Method-Inc-OLD/method-pfc_physical-build/Documentation/Photos/side-module.jpg

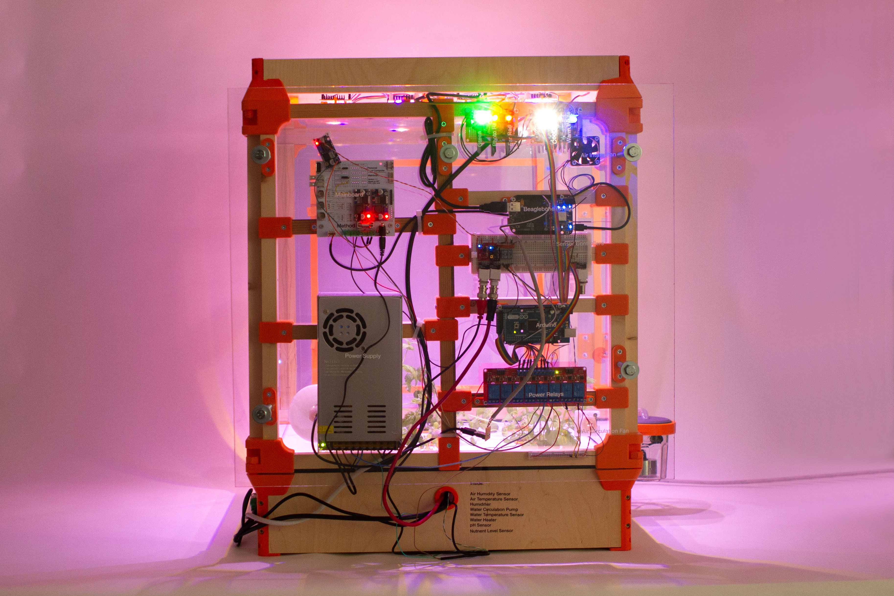
Documentation/Photos/side-module.jpg
