Method-Inc-OLD/method-pfc_physical-build/Documentation/~Working Files/pfc-back-view.jpg

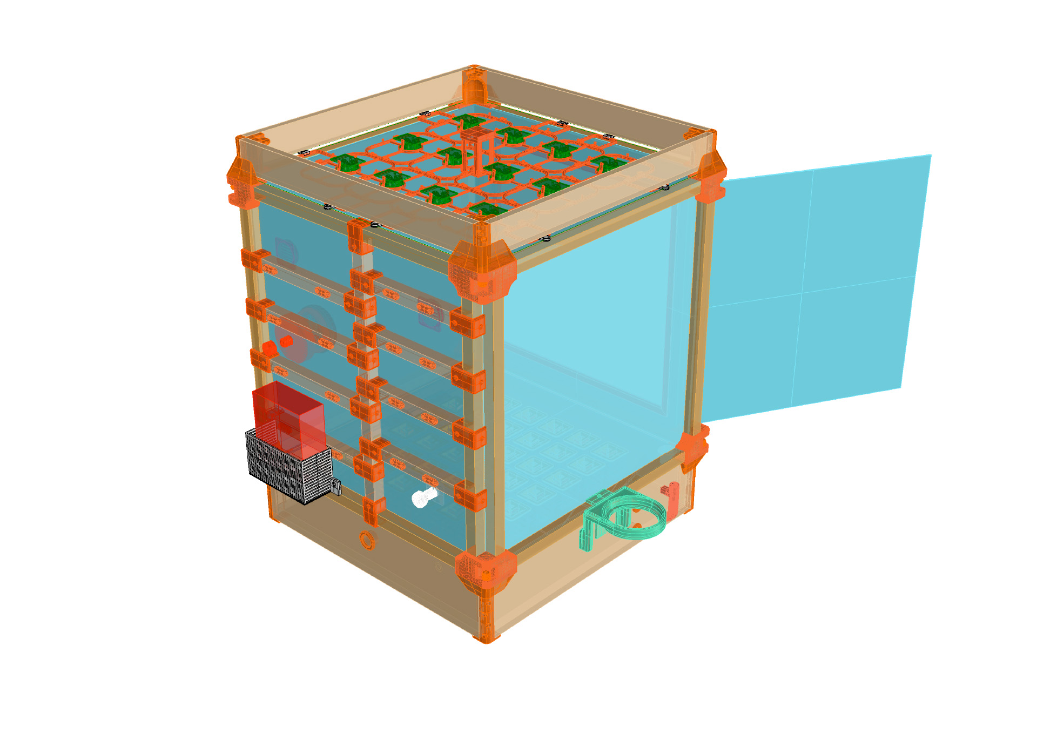
Documentation/~Working Files/pfc-back-view.jpg
