Method-Inc-OLD/method-pfc_physical-build/Documentation/~Working Files/pfc-front-view.jpg

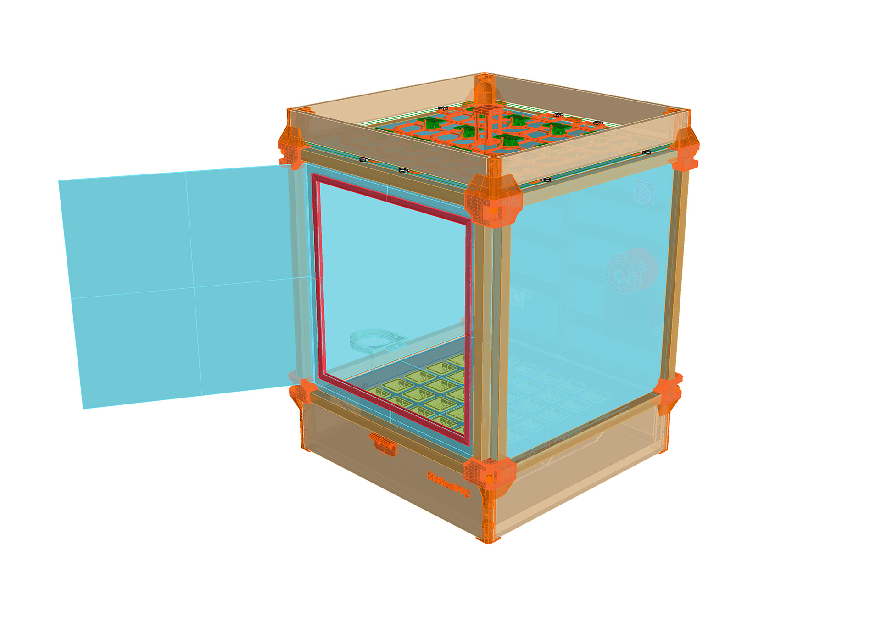
Documentation/~Working Files/pfc-front-view.jpg
