Method-Inc-OLD/method-pfc_physical-build/Electrical/Air Sensor/Air Sensor Schematic.png

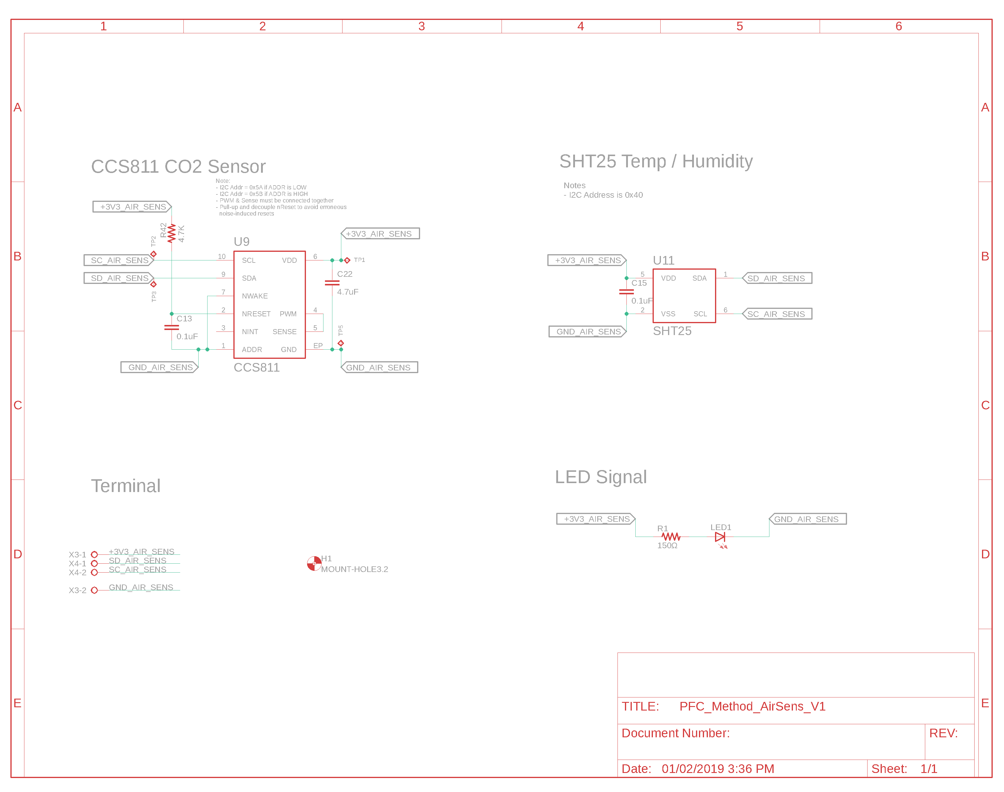
Electrical/Air Sensor/Air Sensor Schematic.png
