Method-Inc-OLD/method-pfc_physical-build/Electrical/Lighting Node + Driver/Lighting Node + Driver Schematic.png

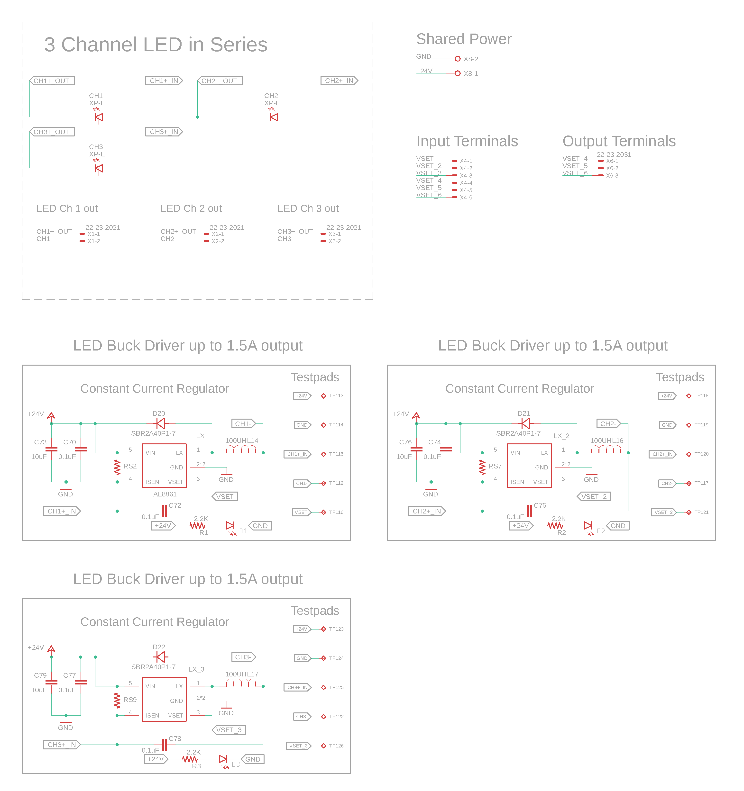
Electrical/Lighting Node + Driver/Lighting Node + Driver Schematic.png
