Method-Inc-OLD/method-pfc_physical-build/Electrical/Lighting Node/Lighting Node Schematic.png

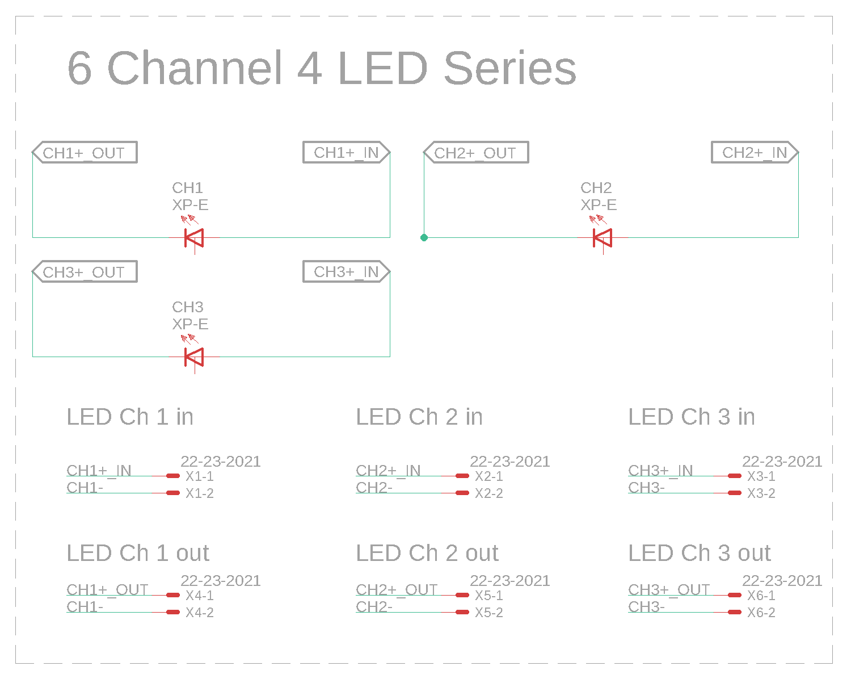
Electrical/Lighting Node/Lighting Node Schematic.png
