Method-Inc-OLD/method-pfc_physical-build/Electrical/Mainboard/Mainboard Schematic.png

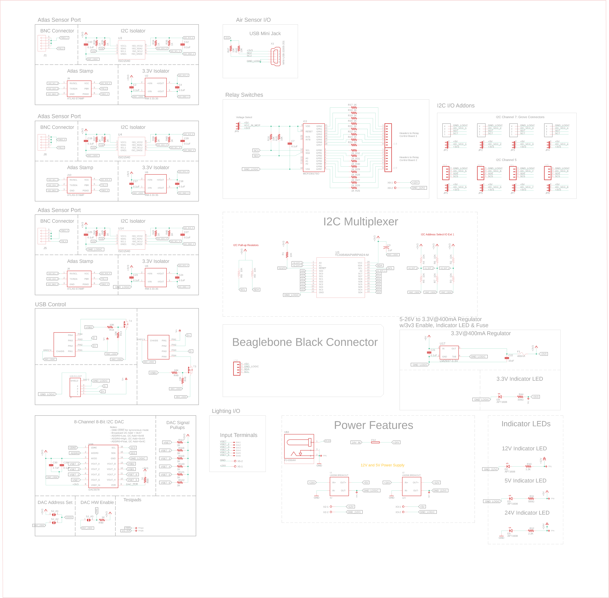
Electrical/Mainboard/Mainboard Schematic.png
