Method-Inc-OLD/method-pfc_physical-build/Mechanical/Middle Module/STL for 3D printing/M.05 - Circulation Fan Mount (2 of 2).stl

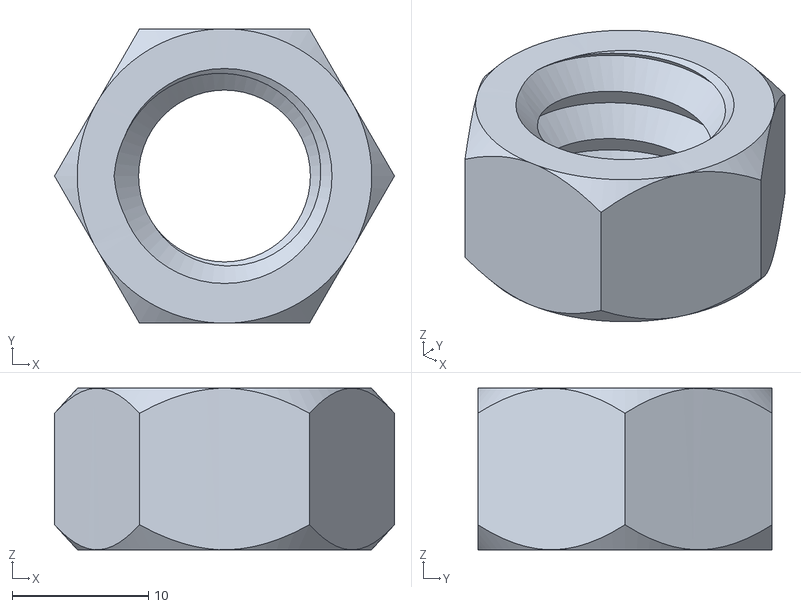
[picture p29: CAD file, 2019-05-31]
Mechanical/Middle Module/STL for 3D printing/M.05 - Circulation Fan Mount (2 of 2).stl
24.9 x 21.6 x 11.8
