Method-Inc-OLD/method-pfc_physical-build/Mechanical/Middle Module/STL for 3D printing/M.07 - Door Lock /files/Fecho_001-16.stl

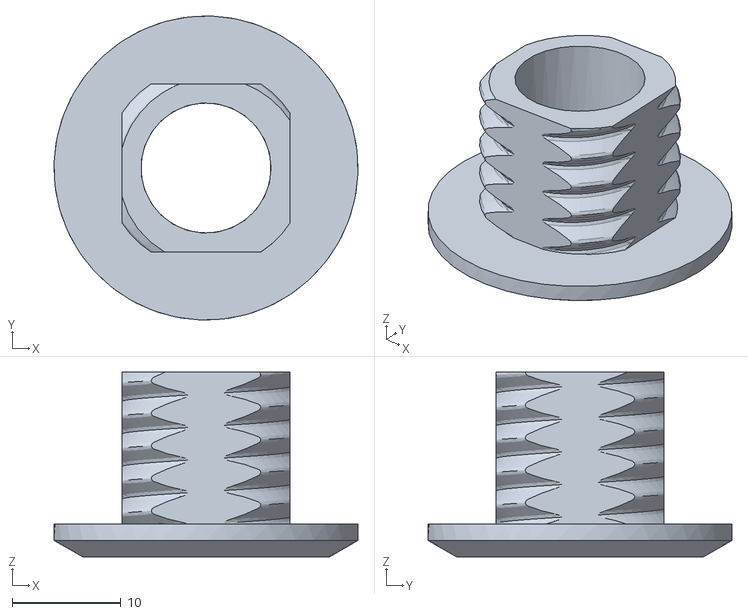
[picture p30: CAD file, 2019-05-31]
Mechanical/Middle Module/STL for 3D printing/M.07 - Door Lock /files/Fecho_001-16.stl
28.0 x 28.0 x 17.0
