Method-Inc-OLD/method-pfc_physical-build/Mechanical/Top Module/STL for 3D Printing/T.01 - Top Corner Connector.stl

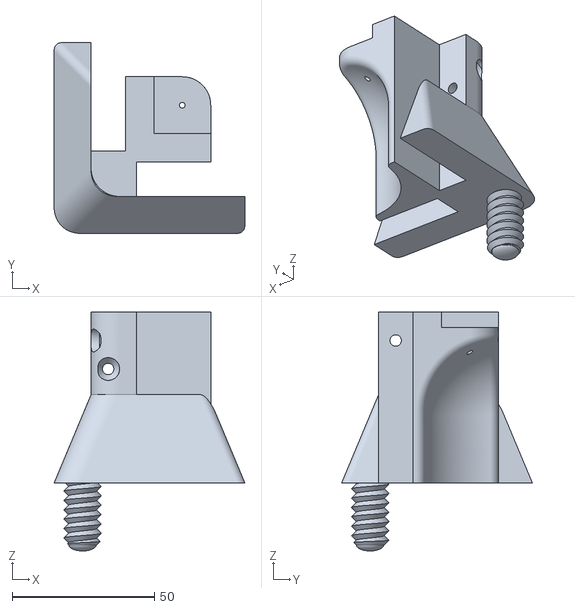
[picture p31: CAD file, 2019-05-31]
Mechanical/Top Module/STL for 3D Printing/T.01 - Top Corner Connector.stl
67.0 x 67.0 x 83.9
