Method-Inc-OLD/method-pfc_physical-build/Mechanical/Bottom Module/STL for 3D Printing/B.02.B - Bottom Corner Connector, Door, Right (1 of 2).stl

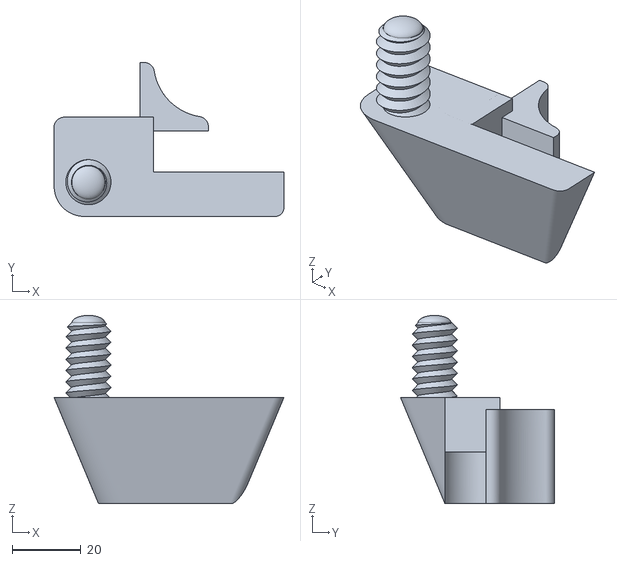
[picture p32: CAD file, 2019-05-31]
Mechanical/Bottom Module/STL for 3D Printing/B.02.B - Bottom Corner Connector, Door, Right (1 of 2).stl
67.1 x 45.0 x 54.9
