Method-Inc-OLD/method-pfc_physical-build/Mechanical/Middle Module/STL for 3D printing/M.01 - Middle Corner Connector.stl

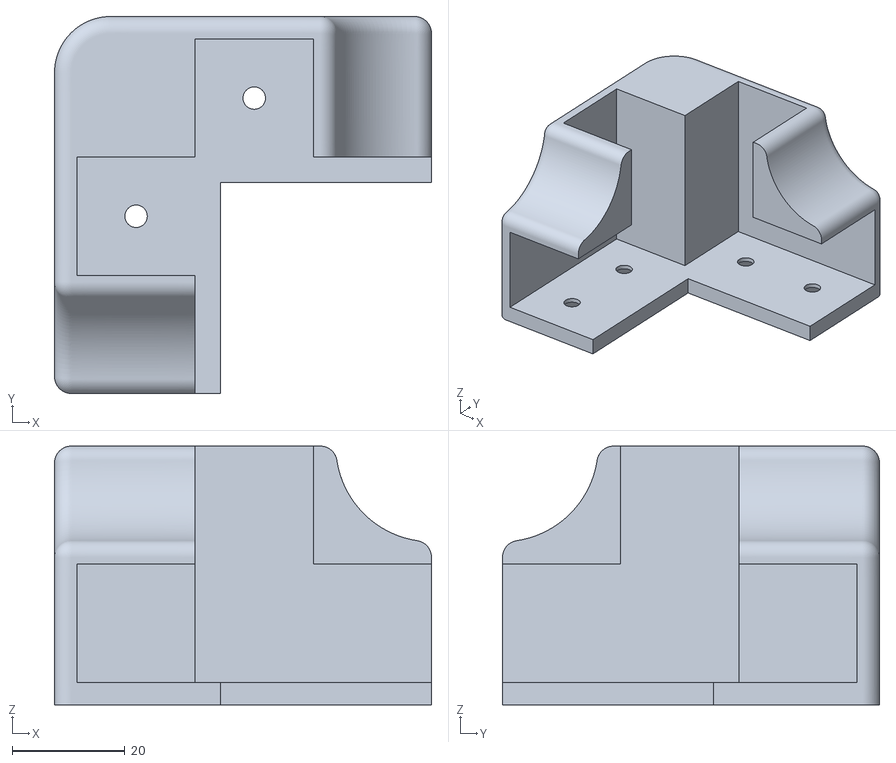
[picture p33: CAD file, 2019-05-31]
Mechanical/Middle Module/STL for 3D printing/M.01 - Middle Corner Connector.stl
67.0 x 67.0 x 46.0
