Method-Inc-OLD/method-pfc_physical-build/Mechanical/Middle Module/STL for 3D printing/M.07 - Door Lock /files/Fecho_002-16.stl

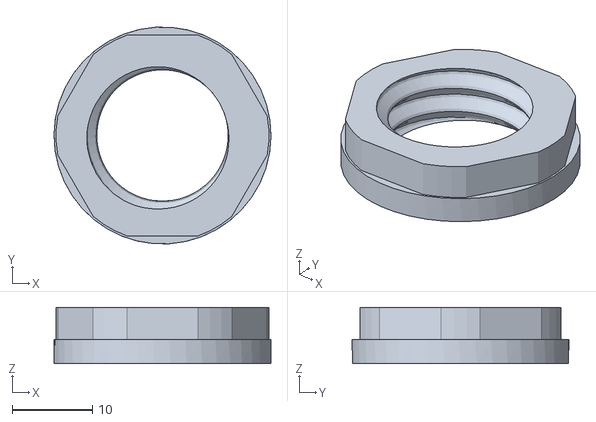
[picture p34: CAD file, 2019-05-31]
Mechanical/Middle Module/STL for 3D printing/M.07 - Door Lock /files/Fecho_002-16.stl
27.0 x 26.9 x 7.00
