Method-Inc-OLD/method-pfc_physical-build/Mechanical/Top Module/STL for 3D Printing/T.02.B - Lighting Board Mount, Camera Holder.stl

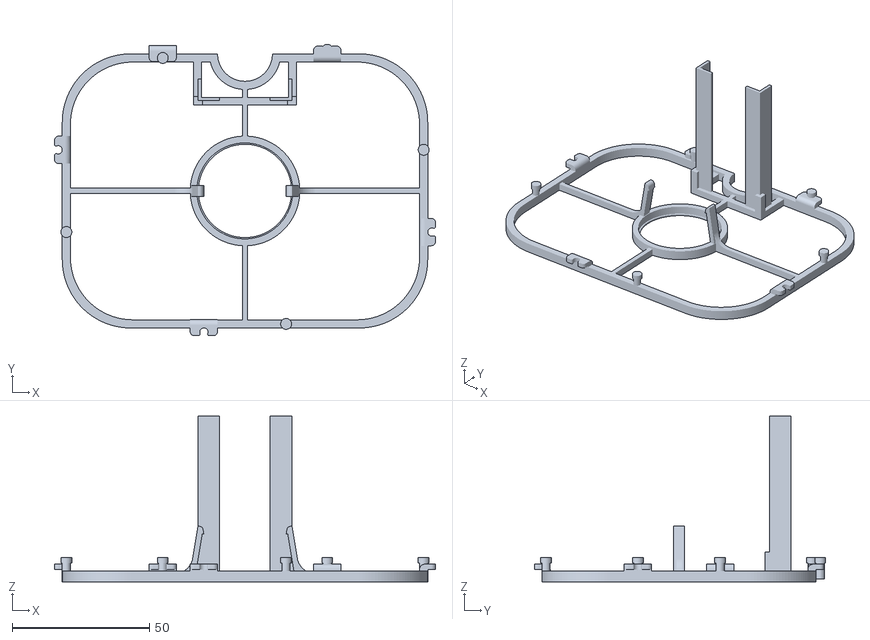
[picture p35: CAD file, 2019-05-31]
Mechanical/Top Module/STL for 3D Printing/T.02.B - Lighting Board Mount, Camera Holder.stl
139.0 x 106.3 x 60.5
