Method-Inc-OLD/method-pfc_physical-build/Mechanical/Bottom Module/STL for 3D Printing/B.07 - Atlas Sensor Holder.stl

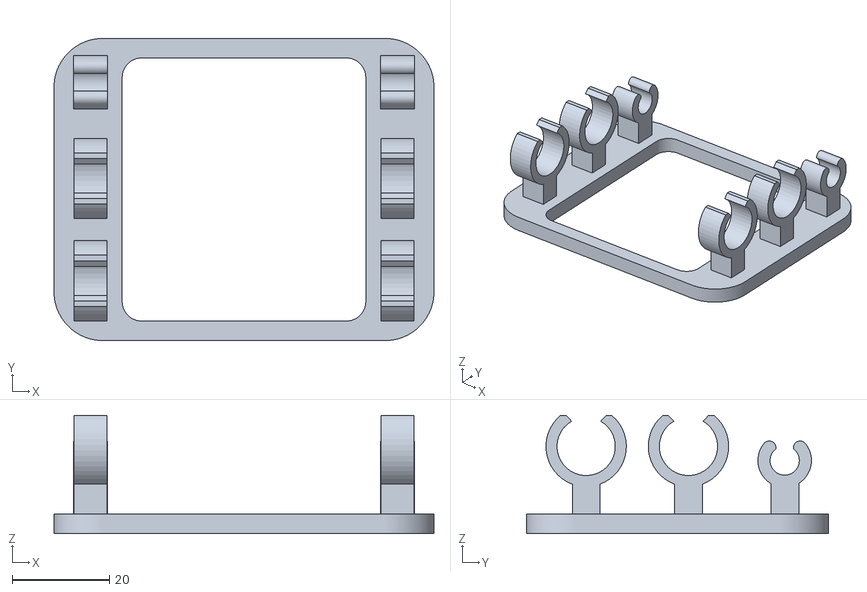
[picture p36: CAD file, 2019-05-31]
Mechanical/Bottom Module/STL for 3D Printing/B.07 - Atlas Sensor Holder.stl
78.0 x 62.0 x 24.3
