Method-Inc-OLD/method-pfc_physical-build/Mechanical/Middle Module/STL for 3D printing/M.03.C - Frame Edge, Bottom Right.stl

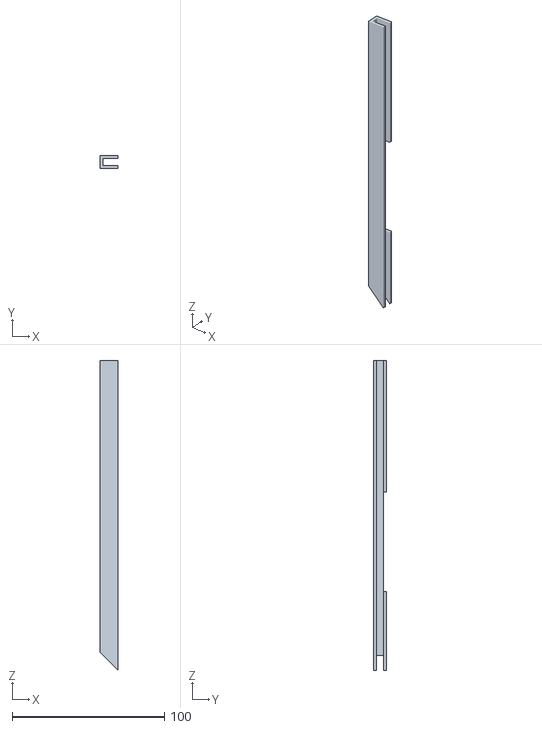
[picture p37: CAD file, 2019-05-31]
Mechanical/Middle Module/STL for 3D printing/M.03.C - Frame Edge, Bottom Right.stl
12.0 x 8.60 x 203.5
