Method-Inc-OLD/method-pfc_physical-build/Mechanical/Middle Module/STL for 3D printing/M.07 - Door Lock /files/Fecho_003.stl

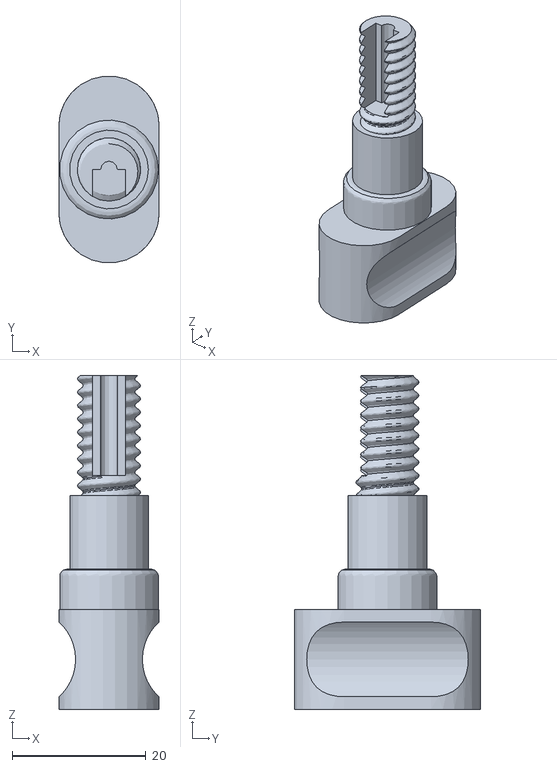
[picture p38: CAD file, 2019-05-31]
Mechanical/Middle Module/STL for 3D printing/M.07 - Door Lock /files/Fecho_003.stl
15.0 x 27.9 x 50.0
