Method-Inc-OLD/method-pfc_physical-build/Mechanical/Top Module/STL for 3D Printing/T.02.A - Lighting Board Mount.stl

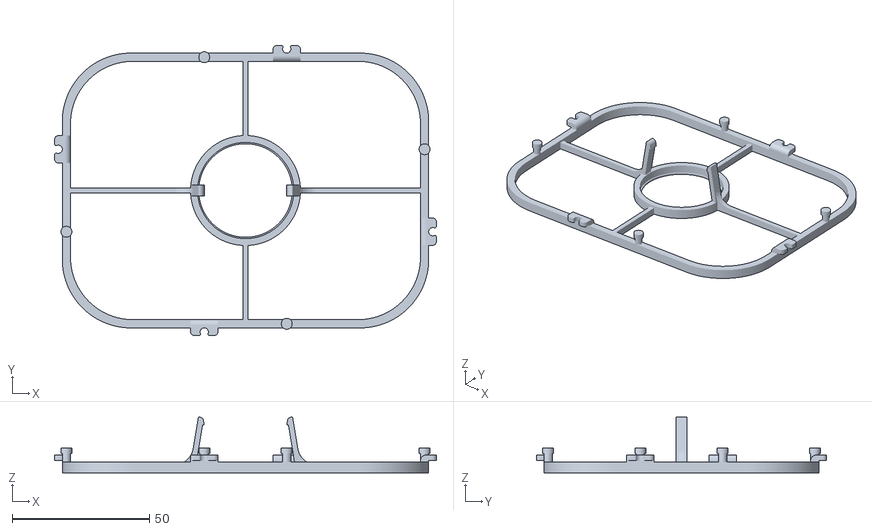
[picture p39: CAD file, 2019-05-31]
Mechanical/Top Module/STL for 3D Printing/T.02.A - Lighting Board Mount.stl
139.0 x 105.6 x 20.3
