Method-Inc-OLD/method-pfc_physical-build/Mechanical/Bottom Module/STL for 3D Printing/B.01.A - Bottom Corner Connector, Left (1 of 2).stl

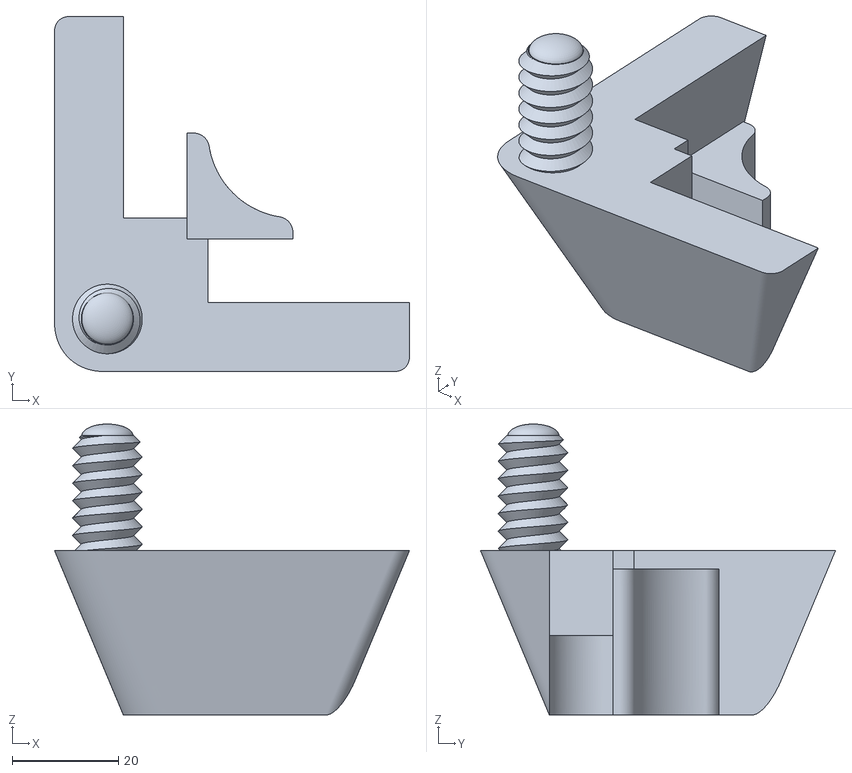
[picture p40: CAD file, 2019-05-31]
Mechanical/Bottom Module/STL for 3D Printing/B.01.A - Bottom Corner Connector, Left (1 of 2).stl
67.0 x 67.0 x 54.9
