Method-Inc-OLD/method-pfc_physical-build/Mechanical/Middle Module/STL for 3D printing/M.07 - Door Lock /files/Fecho_001-18.stl

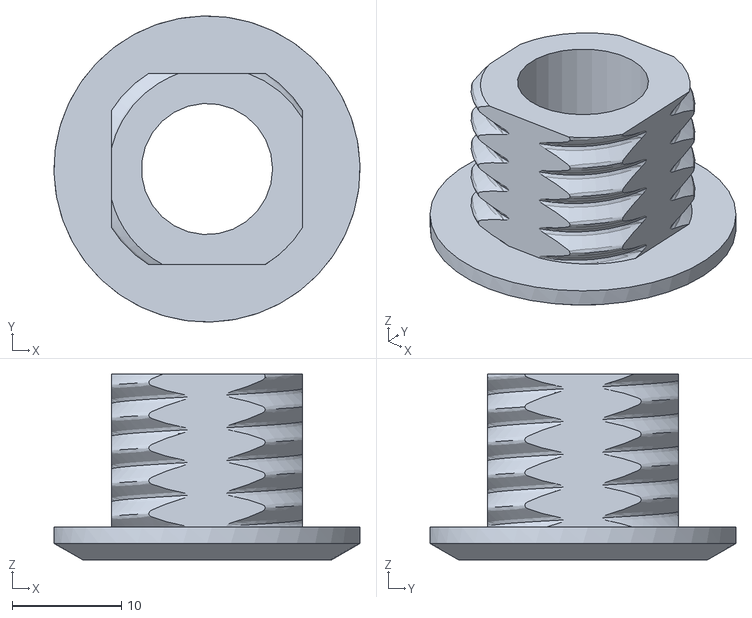
[picture p41: CAD file, 2019-05-31]
Mechanical/Middle Module/STL for 3D printing/M.07 - Door Lock /files/Fecho_001-18.stl
28.0 x 28.0 x 17.0
