Method-Inc-OLD/method-pfc_physical-build/Mechanical/Bottom Module/STL for 3D Printing/B.05v2 - Humidifier Mount (2 of 2).stl

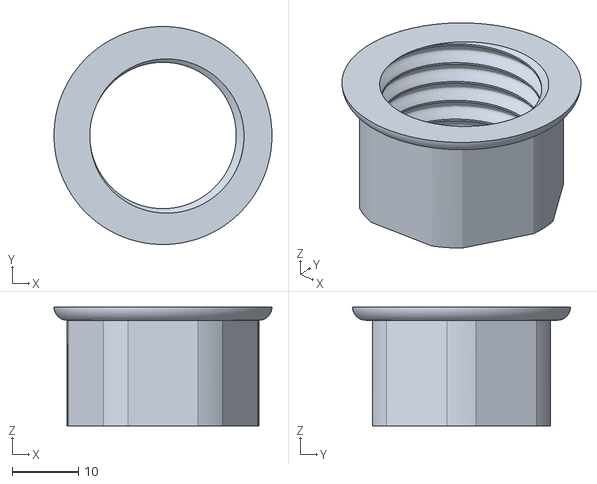
[picture p42: CAD file, 2019-05-31]
Mechanical/Bottom Module/STL for 3D Printing/B.05v2 - Humidifier Mount (2 of 2).stl
33.0 x 33.0 x 18.0
