Method-Inc-OLD/method-pfc_physical-build/Mechanical/Bottom Module/STL for 3D Printing/B.04 - Humidifier Tank Mount.stl

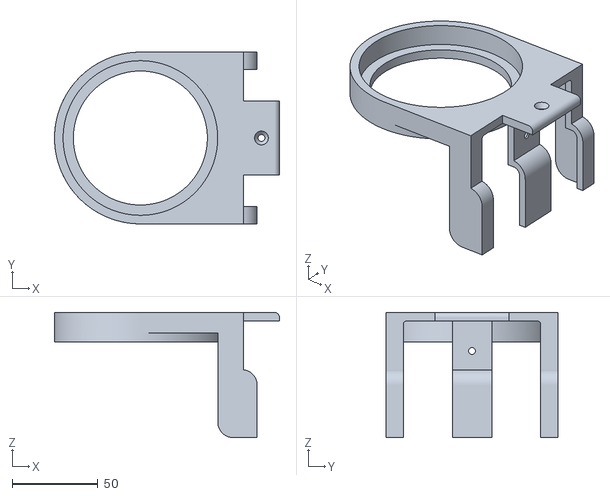
[picture p43: CAD file, 2019-05-31]
Mechanical/Bottom Module/STL for 3D Printing/B.04 - Humidifier Tank Mount.stl
131.0 x 100.0 x 73.0
