Method-Inc-OLD/method-pfc_physical-build/Mechanical/Middle Module/STL for 3D printing/M.07 - Door Lock /files/Fecho_006.stl

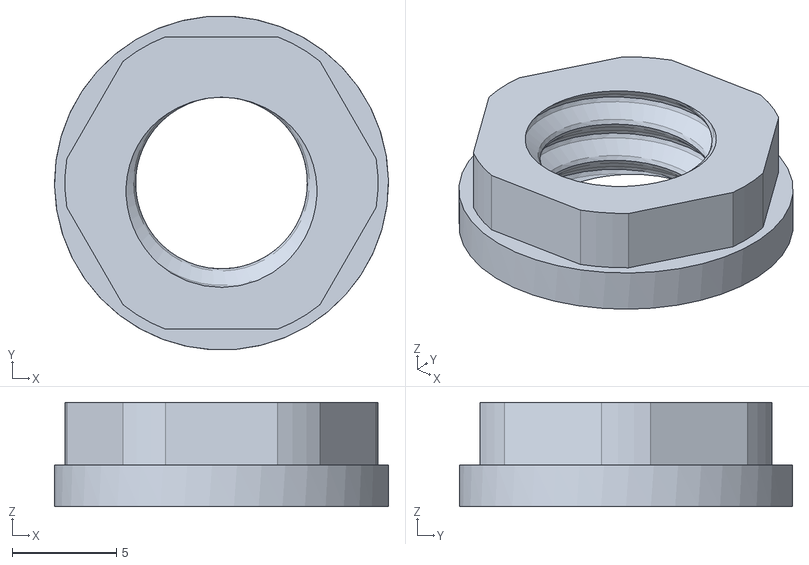
[picture p45: CAD file, 2019-05-31]
Mechanical/Middle Module/STL for 3D printing/M.07 - Door Lock /files/Fecho_006.stl
16.0 x 16.0 x 5.00
