Method-Inc-OLD/method-pfc_physical-build/Mechanical/Bottom Module/STL for 3D Printing/B.11 - Bottom Module – Safety Cover.stl

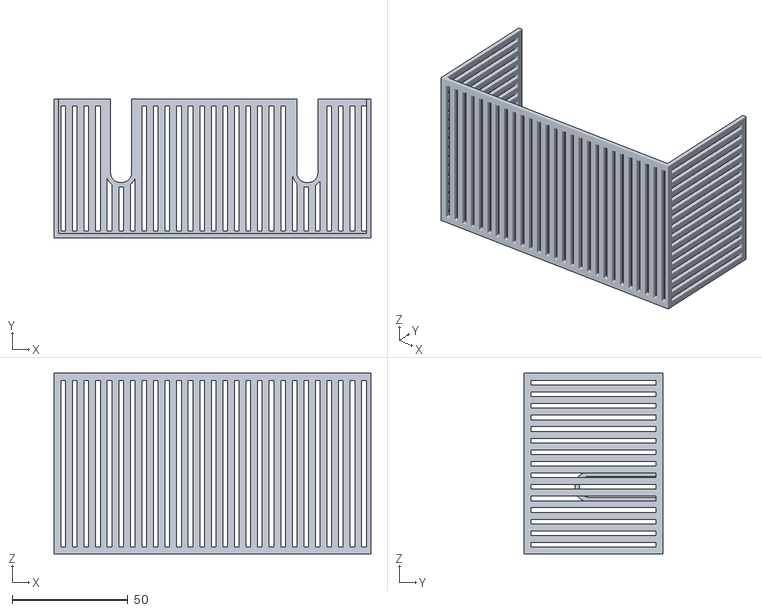
[picture p46: CAD file, 2019-05-31]
Mechanical/Bottom Module/STL for 3D Printing/B.11 - Bottom Module – Safety Cover.stl
137.0 x 60.0 x 78.2
