Method-Inc-OLD/method-pfc_physical-build/Mechanical/Middle Module/STL for 3D printing/M.02 - Air Sensor Bubble (1 of 3).stl

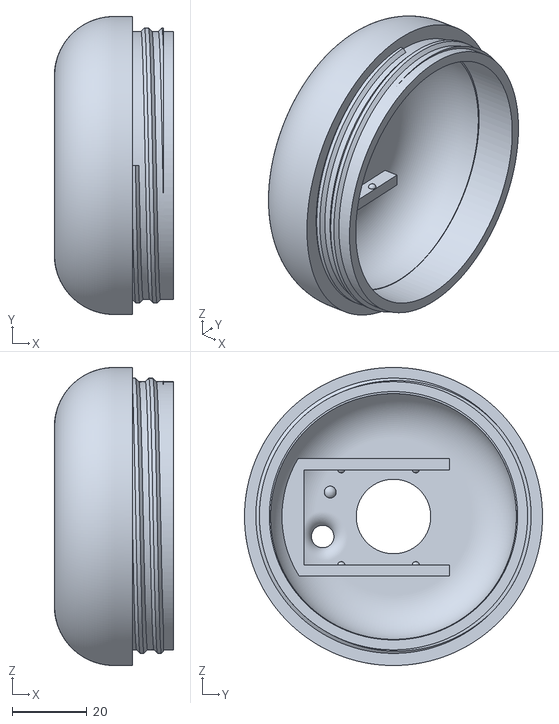
[picture p47: CAD file, 2019-05-31]
Mechanical/Middle Module/STL for 3D printing/M.02 - Air Sensor Bubble (1 of 3).stl
32.0 x 80.0 x 80.0
