Method-Inc-OLD/method-pfc_physical-build/Mechanical/Bottom Module/STL for 3D Printing/B.01.B - Bottom Corner Connector, Right (2 of 2).stl

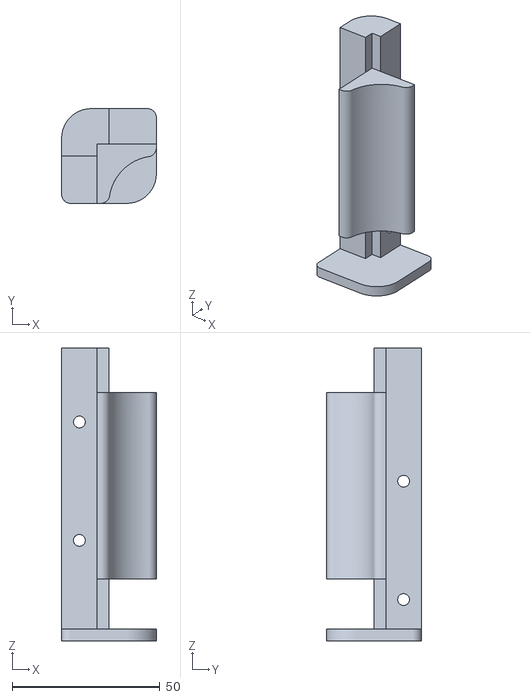
[picture p49: CAD file, 2019-05-31]
Mechanical/Bottom Module/STL for 3D Printing/B.01.B - Bottom Corner Connector, Right (2 of 2).stl
32.0 x 32.0 x 99.0
