Method-Inc-OLD/method-pfc_physical-build/Mechanical/Bottom Module/STL for 3D Printing/B.05v1 - Humidifier Mount (1 of 2).stl

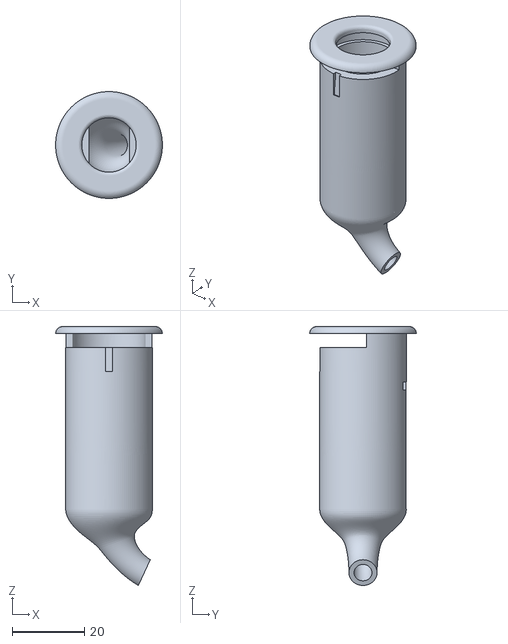
[picture p51: CAD file, 2019-05-31]
Mechanical/Bottom Module/STL for 3D Printing/B.05v1 - Humidifier Mount (1 of 2).stl
29.6 x 29.6 x 71.8
