Method-Inc-OLD/method-pfc_physical-build/Mechanical/Bottom Module/STL for 3D Printing/B.09 - Name plate.stl

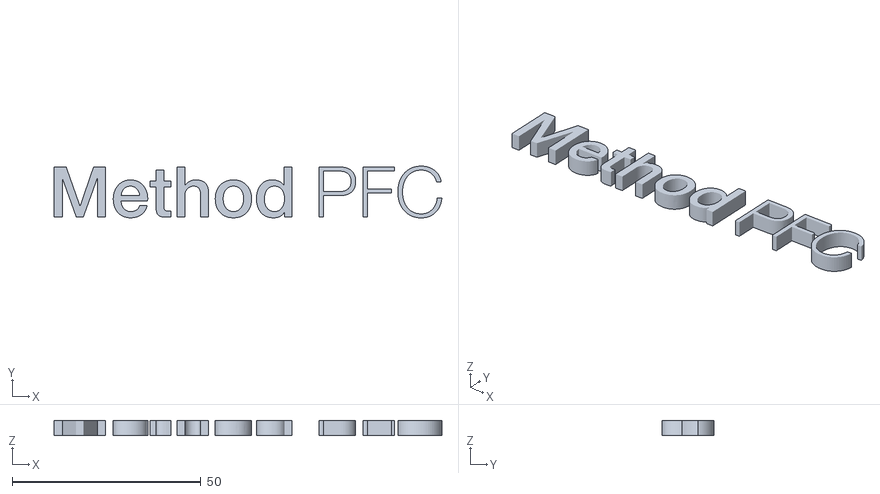
[picture p52: CAD file, 2019-05-31]
Mechanical/Bottom Module/STL for 3D Printing/B.09 - Name plate.stl
102.8 x 13.7 x 4.00
