Method-Inc-OLD/method-pfc_physical-build/Mechanical/Bottom Module/STL for 3D Printing/B.03 - Feeding Tube Holder.stl

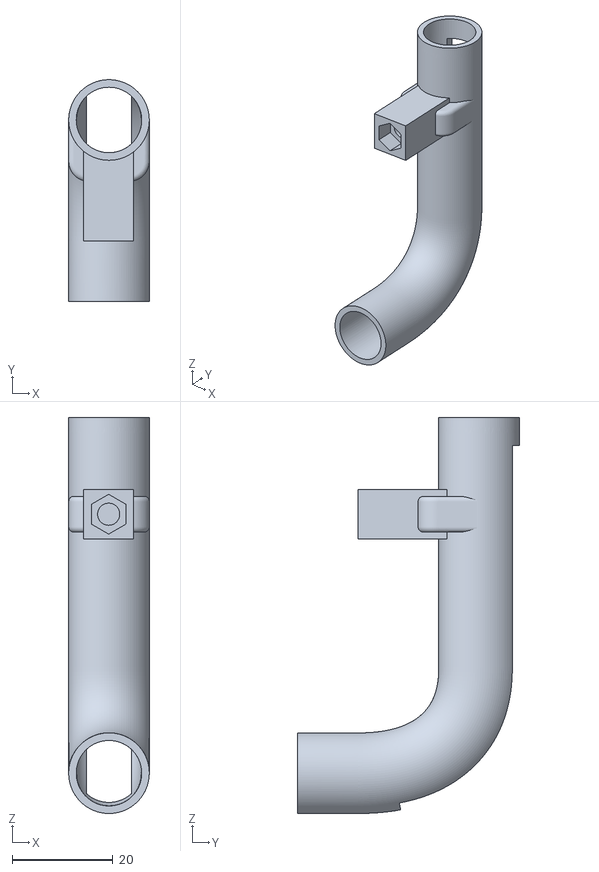
[picture p53: CAD file, 2019-05-31]
Mechanical/Bottom Module/STL for 3D Printing/B.03 - Feeding Tube Holder.stl
16.0 x 44.0 x 78.6
