Method-Inc-OLD/method-pfc_physical-build/Mechanical/Bottom Module/STL for 3D Printing/B.10.B - Rivet, Large, for Wiring.stl

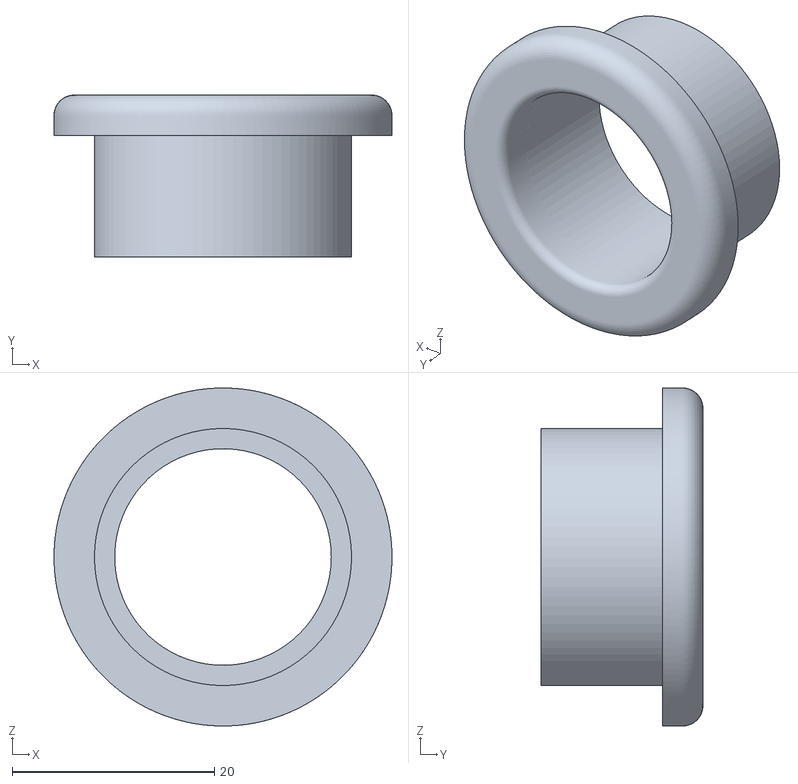
[picture p54: CAD file, 2019-05-31]
Mechanical/Bottom Module/STL for 3D Printing/B.10.B - Rivet, Large, for Wiring.stl
33.4 x 16.0 x 33.4
