Method-Inc-OLD/method-pfc_physical-build/Mechanical/Bottom Module/STL for 3D Printing/B.010.A - Rivet, Small, for Tubing.stl

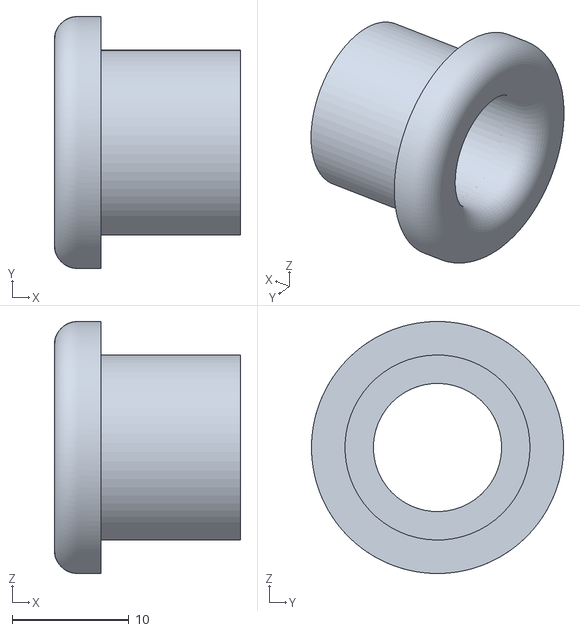
[picture p55: CAD file, 2019-05-31]
Mechanical/Bottom Module/STL for 3D Printing/B.010.A - Rivet, Small, for Tubing.stl
16.0 x 21.6 x 21.6
