Method-Inc-OLD/method-pfc_physical-build/Mechanical/Bottom Module/STL for 3D Printing/B.08 - Door Handle.stl

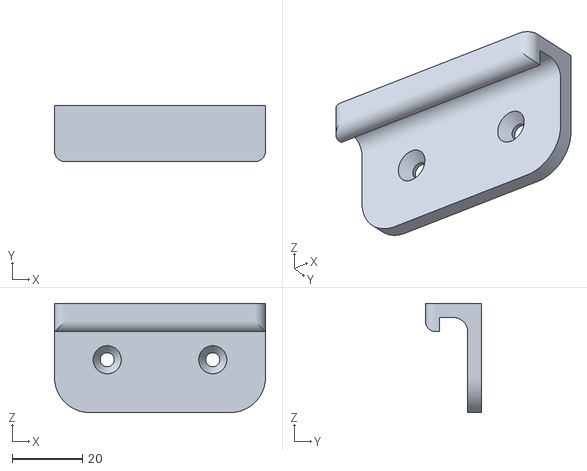
[picture p56: CAD file, 2019-05-31]
Mechanical/Bottom Module/STL for 3D Printing/B.08 - Door Handle.stl
60.0 x 16.0 x 31.0
