Method-Inc-OLD/method-pfc_physical-build/Mechanical/Bottom Module/STL for 3D Printing/B.06 - Rockwool Carriage.stl

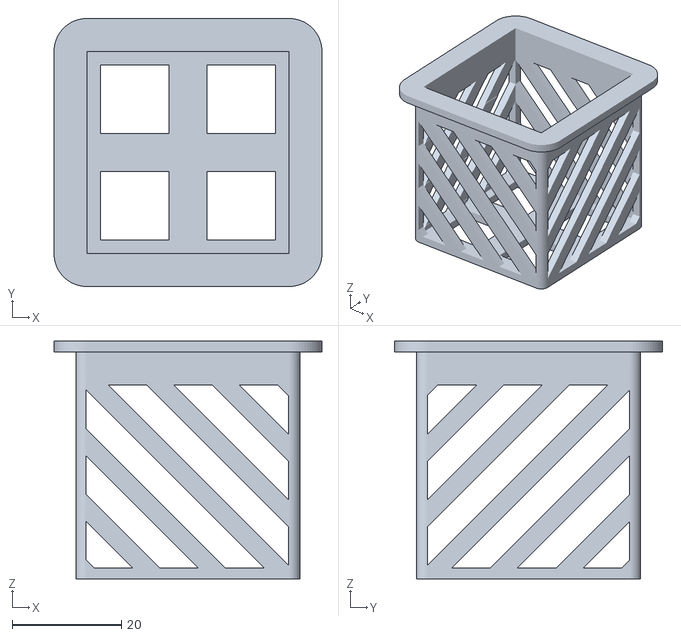
[picture p57: CAD file, 2019-05-31]
Mechanical/Bottom Module/STL for 3D Printing/B.06 - Rockwool Carriage.stl
49.0 x 49.0 x 43.5
