Method-Inc-OLD/method-pfc_physical-build/Mechanical/Bottom Module/STL for 3D Printing/B.05v1 - Humidifier Mount (2 of 2).stl

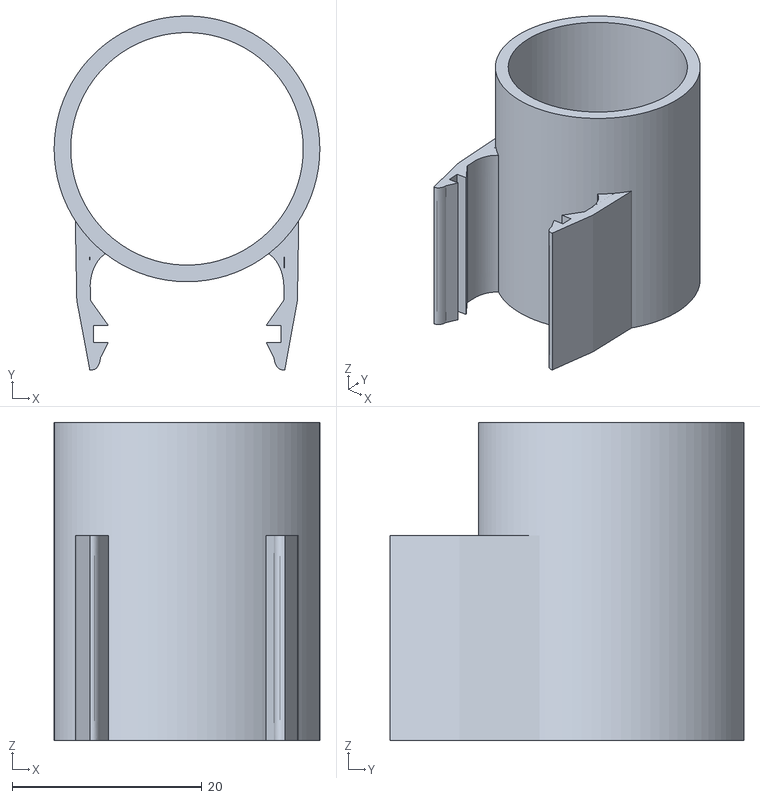
[picture p58: CAD file, 2019-05-31]
Mechanical/Bottom Module/STL for 3D Printing/B.05v1 - Humidifier Mount (2 of 2).stl
28.0 x 37.3 x 33.5
