Method-Inc-OLD/method-pfc_physical-build/Mechanical/Middle Module/STL for 3D printing/M.06 - Door Hinge/images/8f4b54f08936ee00a93d4b04b920801e_preview_featured.jpg

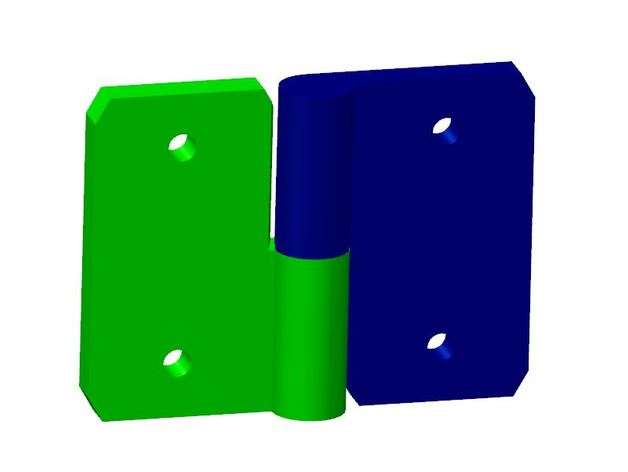
Mechanical/Middle Module/STL for 3D printing/M.06 - Door Hinge/images/8f4b54f08936ee00a93d4b04b920801e_preview_featured.jpg
