Method-Inc-OLD/method-pfc_physical-build/Mechanical/Middle Module/STL for 3D printing/M.06 - Door Hinge/images/fa78f0b6158e9a1c80da4dba1ec0081e_preview_featured.jpg

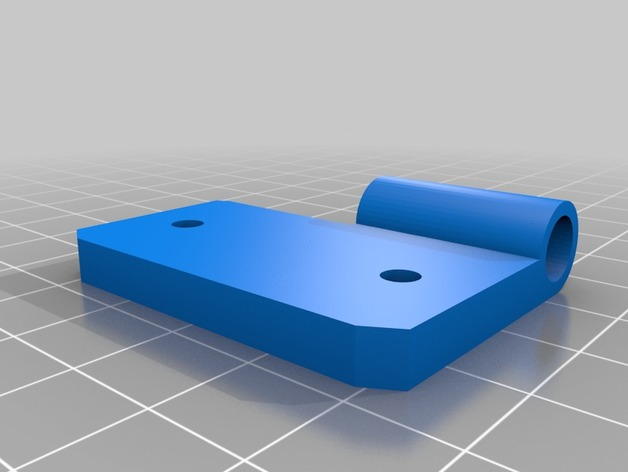
Mechanical/Middle Module/STL for 3D printing/M.06 - Door Hinge/images/fa78f0b6158e9a1c80da4dba1ec0081e_preview_featured.jpg
