Method-Inc-OLD/method-pfc_physical-build/Mechanical/Middle Module/STL for 3D printing/M.07 - Door Lock /images/0bf5f9f50b0dcd644b62373efc88d2cc_preview_featured.jpg

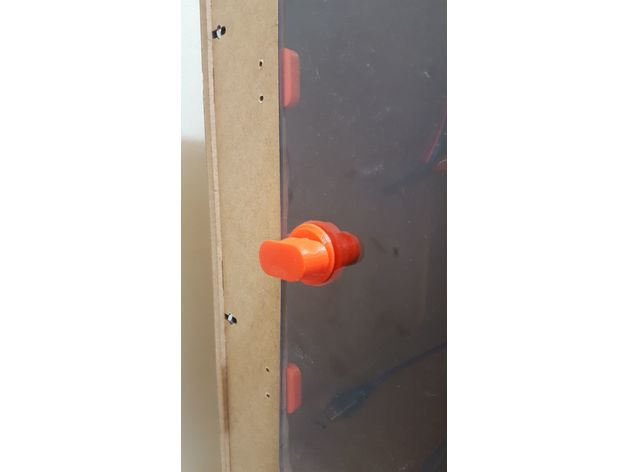
Mechanical/Middle Module/STL for 3D printing/M.07 - Door Lock /images/0bf5f9f50b0dcd644b62373efc88d2cc_preview_featured.jpg
