Method-Inc-OLD/method-pfc_physical-build/Mechanical/Middle Module/STL for 3D printing/M.07 - Door Lock /images/1bd6a7eec26142c094a8899e28941d43_preview_featured.jpg

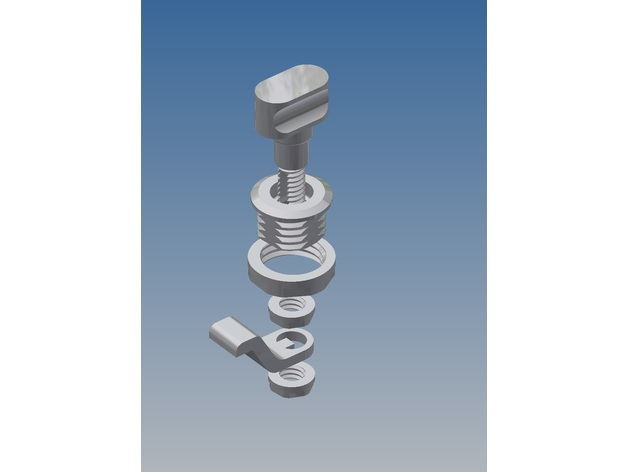
Mechanical/Middle Module/STL for 3D printing/M.07 - Door Lock /images/1bd6a7eec26142c094a8899e28941d43_preview_featured.jpg
