Method-Inc-OLD/method-pfc_physical-build/Mechanical/Middle Module/STL for 3D printing/M.07 - Door Lock /images/43478f30ed899dcd3368a6ff01d97558_preview_featured.jpg

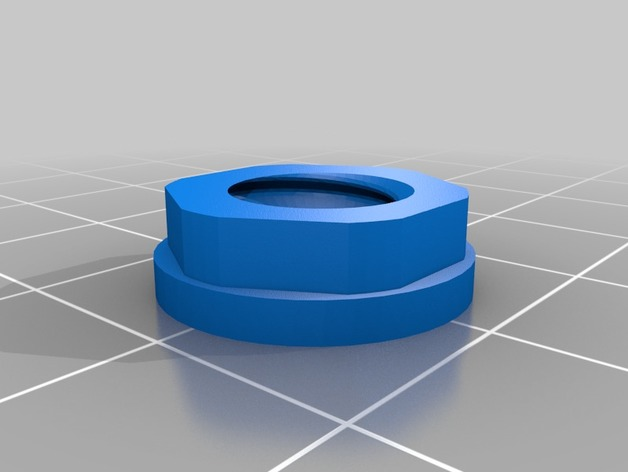
Mechanical/Middle Module/STL for 3D printing/M.07 - Door Lock /images/43478f30ed899dcd3368a6ff01d97558_preview_featured.jpg
