Method-Inc-OLD/method-pfc_physical-build/Mechanical/Middle Module/STL for 3D printing/M.07 - Door Lock /images/0264584c2e0fdf487e41ed4ffffc523d_preview_featured.jpg

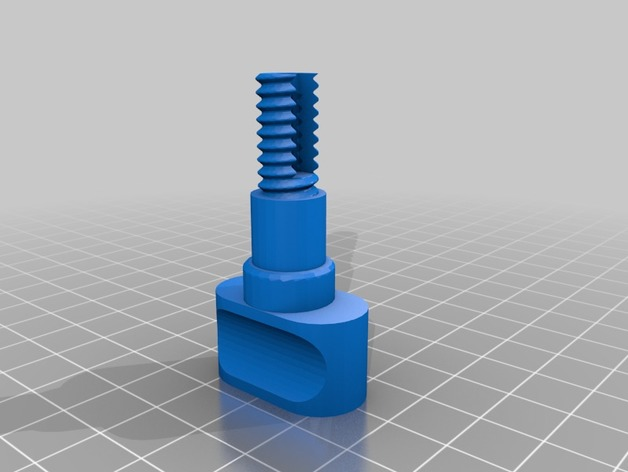
Mechanical/Middle Module/STL for 3D printing/M.07 - Door Lock /images/0264584c2e0fdf487e41ed4ffffc523d_preview_featured.jpg
