Method-Inc-OLD/method-pfc_physical-build/Mechanical/Middle Module/STL for 3D printing/M.07 - Door Lock /images/47724360ff2a16feb44409498bce302b_preview_featured.jpg

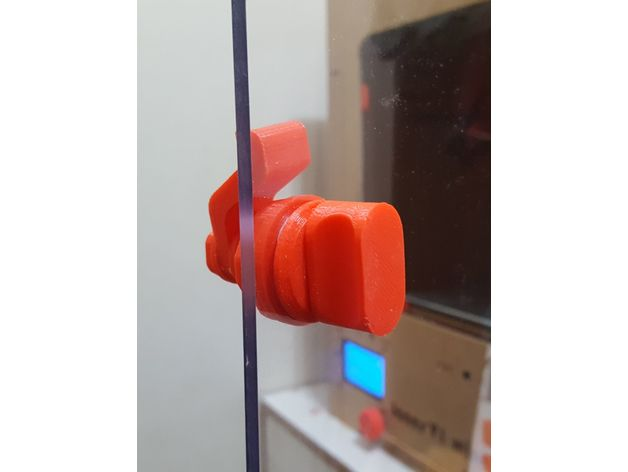
Mechanical/Middle Module/STL for 3D printing/M.07 - Door Lock /images/47724360ff2a16feb44409498bce302b_preview_featured.jpg
