Method-Inc-OLD/method-pfc_physical-build/Mechanical/Middle Module/STL for 3D printing/M.07 - Door Lock /images/f8a6dca50ad46f29d6516d19780ebb39_preview_featured.jpg

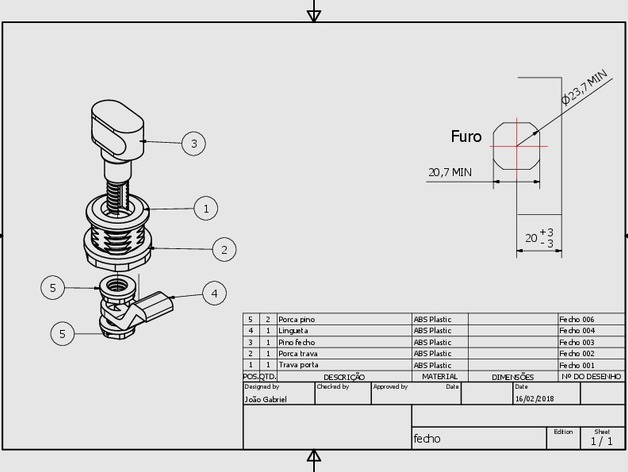
Mechanical/Middle Module/STL for 3D printing/M.07 - Door Lock /images/f8a6dca50ad46f29d6516d19780ebb39_preview_featured.jpg
