Method-Inc-OLD/method-pfc_physical-build/Mechanical/Middle Module/STL for 3D printing/M.07 - Door Lock /images/fad69c18e2e47b85757e2de6763296bf_preview_featured.jpg

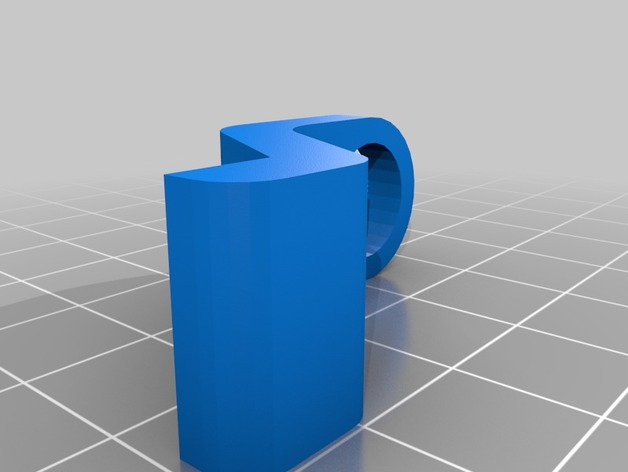
Mechanical/Middle Module/STL for 3D printing/M.07 - Door Lock /images/fad69c18e2e47b85757e2de6763296bf_preview_featured.jpg
